andrewfernie/CNCControl/GRBLPendant/include/lcd_screens.h

#pragma once
//=========================================================
//Project: GRBL Pendant
//Module:  lcd_screens.H     
//=========================================================
//
// Author: Andrew Fernie
// Source code freely released - do with it what you like
//
//=========================================================

extern void DisplayState();
extern void DisplayJogScreen();
